riku-ohyea/EMEC-micromouse/02 test hardware code/09 MM DRIVERS/0208_bot1test02/TOFSensors.py

# Backup function for 3x sensor reading

from machine import Pin, I2C
import time
from PiicoDev_VL53L1X import PiicoDev_VL53L1X

import math

class TOFMultiplexer:
    def __init__(self, bus: int, sda_pin: int, scl_pin: int, mux_addr=0x70, channels=(0,1,2)):
        self.bus = bus
        self.sda = Pin(sda_pin)
        self.scl = Pin(scl_pin)

        # create ONE I2C object for mux control (optional but convenient)
        self.i2c = I2C(self.bus, sda=self.sda, scl=self.scl, freq=100_000)

        self.mux_addr = mux_addr
        self.channels = list(channels)

        self.wallBoundaryDist = 80

        # Additions for TOF header
        self.offset_L = 6.0
        self.offset_R = 6.0
        # optional: reject obviously bad reads
        self.min_valid_mm = -1
        self.max_valid_mm = 50000  # adjust to corridor expectations

        self.sensors = []
        for ch in self.channels:
            self.mux_select(ch)
            time.sleep_ms(10)  # let mux + sensor settle

            # retry init a few times
            sensor = None
            for _ in range(3):
                try:
                    sensor = PiicoDev_VL53L1X(bus=self.bus, sda=self.sda, scl=self.scl, freq=100_000)
                    break
                except OSError:
                    time.sleep_ms(50)
                    self.mux_disable_all()
                    time.sleep_ms(10)
                    self.mux_select(ch)
                    time.sleep_ms(20)

            if sensor is None:
                raise RuntimeError("Failed to init TOF on mux channel {}".format(ch))

            self.sensors.append(sensor)

        self.mux_disable_all()

    def _valid_mm(self, v):
        if v is None:
            return None
        # PiicoDev_VL53L1X.read() can return NaN on I2C error
        try:
            if isinstance(v, float) and math.isnan(v):
                return None
        except:
            pass
        try:
            v = float(v)
        except:
            return None
        if v < self.min_valid_mm or v > self.max_valid_mm:
            return None
        return v

    def mux_select(self, channel: int):
        self.i2c.writeto(self.mux_addr, bytes([1 << channel]))

    def mux_disable_all(self):
        self.i2c.writeto(self.mux_addr, b"\x00")

    # def get_distance_mm(self, index: int) -> int:
    #     ch = self.channels[index]
    #     self.mux_select(ch)
    #     return self.sensors[index].read()
    
    def get_distance_mm(self, index: int):
        ch = self.channels[index]
        self.mux_select(ch)
        raw = self.sensors[index].read()
        return self._valid_mm(raw)
    
    def has_both_side_walls(self):
        L = self.get_distance_mm(0)
        R = self.get_distance_mm(2)
        if L is None or R is None:
            return False
        return (L < self.wallBoundaryDist) and (R < self.wallBoundaryDist)
    
    def side_error_mm(self):
        """Return L_cal - R_cal (positive => left reads farther than right)."""
        L = self.get_distance_mm(0)
        R = self.get_distance_mm(2)
        if L is None or R is None:
            return None
        L_cal = L + self.offset_L
        R_cal = R + self.offset_R
        return (L_cal - R_cal)
