riku-ohyea/EMEC-micromouse/02 test hardware code/09 MM DRIVERS/0208_bot1test02/Maze.py

# Maze.py (MicroPython-friendly)
import API
from Direction import Direction

class Maze:
    def __init__(self, width, height):
        self.width = width
        self.height = height

        # Initialize walls without itertools.product
        self.walls = {}
        for x in range(width):
            for y in range(height):
                self.walls[(x, y)] = set()

        # Boundary walls
        for (x, y) in self.walls:
            if x == 0:
                self.setWall((x, y), Direction.WEST)
            if y == 0:
                self.setWall((x, y), Direction.SOUTH)
            if x == width - 1:
                self.setWall((x, y), Direction.EAST)
            if y == height - 1:
                self.setWall((x, y), Direction.NORTH)

        # Calculate center
        cx = width // 2
        cy = height // 2
        self.center = {(cx, cy)}
        if width % 2 == 0:
            self.center.add((cx - 1, cy))
        if height % 2 == 0:
            self.center.add((cx, cy - 1))
        if height % 2 == 0 and width % 2 == 0:
            self.center.add((cx - 1, cy - 1))

    def contains(self, position):
        return position in self.walls

    def inCenter(self, position):
        return position in self.center

    def getWall(self, position, direction):
        return direction in self.walls[position]

    def setWall(self, position, direction):
        self.walls[position].add(direction)
        # API.setWall(position[0], position[1], Direction.VALUE[direction])
